LeeMakeKR/1D_Arcade_Game/Arduino/1DarcadeV1.0/Logo1DArcade.h

#pragma once

// 이 파일은 pics/logo2header.py가 자동 생성한 것이다. 직접 수정하지 말 것.
// 원본 Logo1DArcade.h 를 3종 토큰 RLE로 압축했다.
//   압축 전 35520 bytes -> 압축 후 11973 bytes (33.7%)
//
// 토큰 1바이트 = [상위 2비트 종류][하위 6비트 개수 n]
//     00 n : 리터럴  - 뒤에 uint16(LE) n개
//     01 n : 투명    - 0x0000 픽셀 n개(데이터 없음, 건너뛴다)
//     10 n : 반복    - 뒤의 uint16(LE) 1개를 n번
//   0x00은 "리터럴 0개"라 나올 수 없어 스트림 끝 표시로 쓴다.

#include <Adafruit_GFX.h>

static const uint16_t LOGO_1D_ARCADE_W = 148;
static const uint16_t LOGO_1D_ARCADE_H = 120;
static const uint32_t LOGO_1D_ARCADE_PIXELS = 17760UL;

static const uint8_t LOGO_1D_ARCADE_RLE[] = {
  0x7F, 0x7F, 0x7F, 0x7F, 0x7F, 0x7F, 0x7F, 0x7F, 0x7F, 0x7F, 0x7F, 0x7F, 0x7F, 0x7F, 0x7F, 0x7F,
  0x7F, 0x7F, 0x7F, 0x7F, 0x7F, 0x7F, 0x7F, 0x7F, 0x7F, 0x7F, 0x76, 0x0A, 0x20, 0x08, 0x20, 0x08,
  0x40, 0x10, 0x40, 0x10, 0x20, 0x10, 0x20, 0x10, 0x40, 0x10, 0x20, 0x10, 0x20, 0x08, 0x20, 0x08,
  0x7F, 0x7F, 0x4A, 0x0D, 0x20, 0x00, 0x20, 0x08, 0x40, 0x18, 0x60, 0x20, 0x80, 0x20, 0x80, 0x28,
  0x80, 0x28, 0x60, 0x28, 0x80, 0x28, 0x60, 0x20, 0x60, 0x18, 0x40, 0x10, 0x20, 0x08, 0x7F, 0x7F,
  0x49, 0x06, 0x20, 0x08, 0x60, 0x18, 0x01, 0x41, 0xE5, 0xAA, 0xE4, 0xB2, 0xE4, 0xB2, 0x84, 0xC4,
  0xB2, 0x04, 0xC4, 0xAA, 0x22, 0x49, 0x40, 0x18, 0x20, 0x08, 0x7F, 0x7F, 0x47, 0x10, 0x20, 0x08,
  0x60, 0x18, 0xC0, 0x30, 0xC2, 0x61, 0x87, 0xFC, 0x66, 0xFC, 0x25, 0xFC, 0xC5, 0xFB, 0xA5, 0xFB,
  0x85, 0xFB, 0xA5, 0xFB, 0xE5, 0xFB, 0xA2, 0x71, 0x60, 0x28, 0x40, 0x18, 0x20, 0x08, 0x7F, 0x7F,
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
        color = (uint16_t)p[0] | ((uint16_t)p[1] << 8);
        p += 2;
      }
      canvas.drawPixel(ox + (int16_t)(px % LOGO_1D_ARCADE_W),
                       oy + (int16_t)(px / LOGO_1D_ARCADE_W), color);
      px++;
    }
  }
}
